james8268/Buggy/Code/Arduino mega code/Arduino_Mega_Code/RFID.h

#ifndef RFID_h
#define RFID_h  //create our header file



class RFIDclass   //setup the operation class
{

public:
    RFIDclass();

    void RFIDsetup();    //here is the setup function and challenge function. 
    bool RFID_challenge();
    
};

extern RFIDclass RFID;

#endif
