james8268/Buggy/Code/Arduino mega code/Arduino_Mega_Code/Comms.h

//our communication header file. 

#ifndef Comms_h      
#define Comms_h   //define our header 

class Commsclass      //class name
{
public:
Commsclass();
    void SETUP();          //we have only two functions, the setup and one where it will read the message sent to the serial port from the bluetooth/WiFi serial port 
    void read_message();



};

extern Commsclass Comms;

#endif
