james8268/Buggy/Code/Bluetooth/Bluetooth/encrypt.h

#ifndef encrypt_h
#define encrypt_h  //create our header file



class encryptclass   //setup our ultrasound class
{

public:
    encryptclass();
void rot(int inByte);
void SETUP();


};

extern encryptclass encrypt;

#endif
